Creatronic/DellSupplyConverter/Photos/IMG_20211026_142526_1.jpg

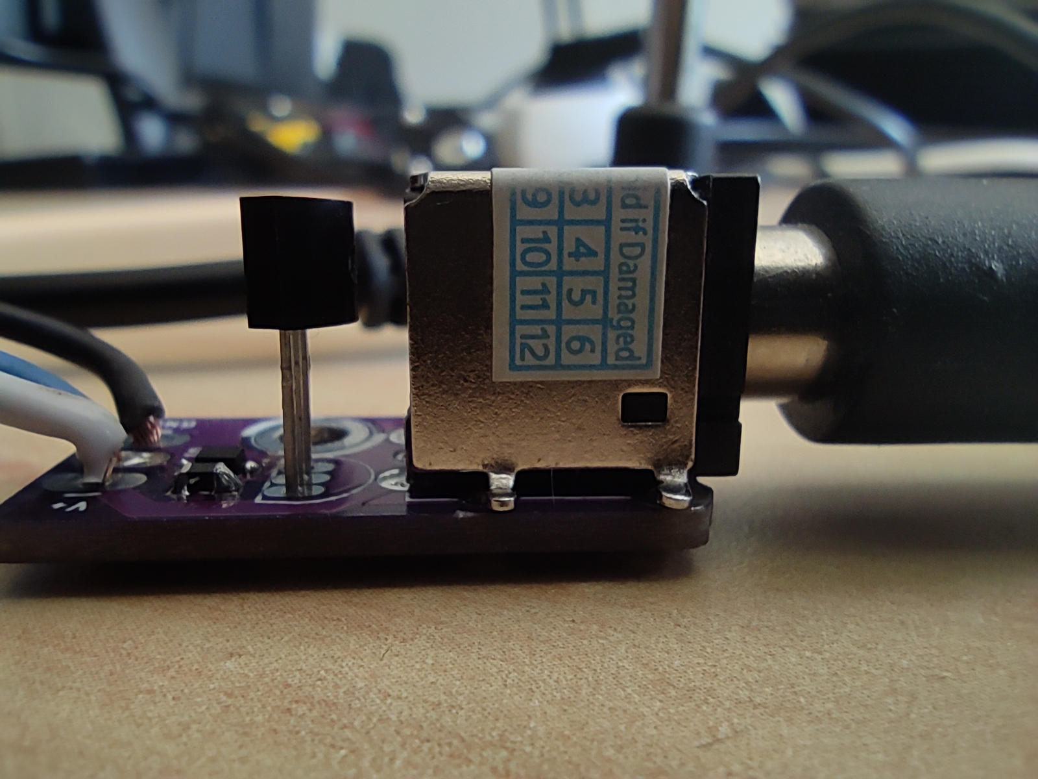
Photos/IMG_20211026_142526_1.jpg
