Creatronic/DellSupplyConverter/Photos/IMG_20211026_142629.jpg

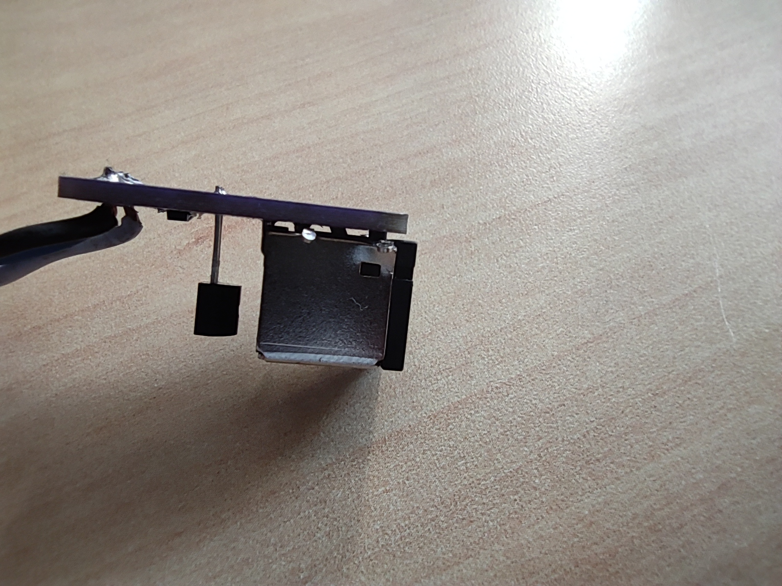
Photos/IMG_20211026_142629.jpg
