Creatronic/DellSupplyConverter/Photos/IMG_20211026_142632_1.jpg

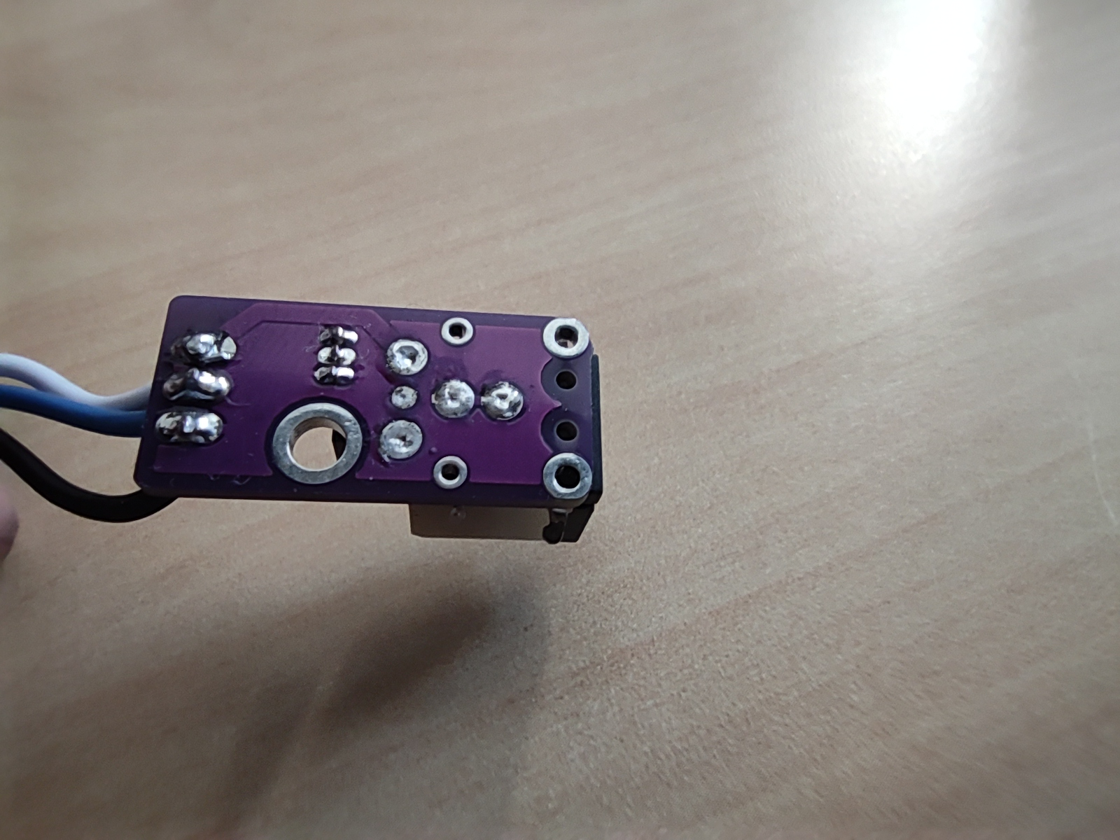
Photos/IMG_20211026_142632_1.jpg
