Creatronic/DellSupplyConverter/Photos/IMG_20211026_142641_1.jpg

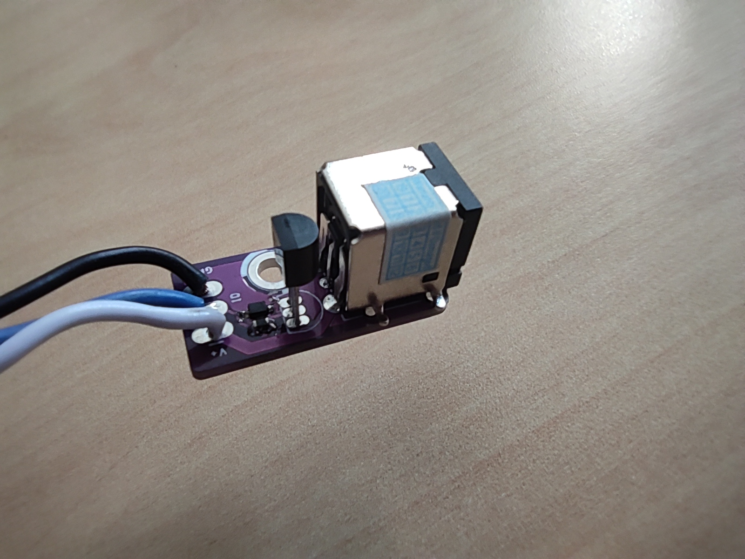
Photos/IMG_20211026_142641_1.jpg
